Natotj/OctoMix/Documents/Display_Mount_Ideas.png

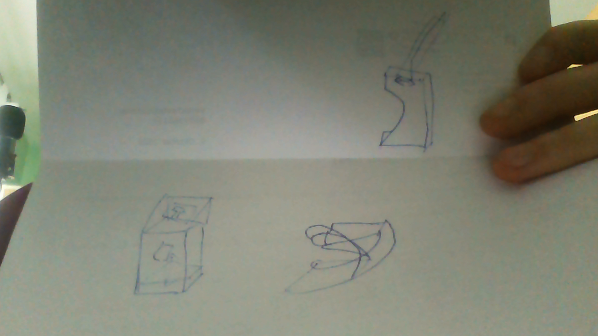
Documents/Display_Mount_Ideas.png
