Natotj/OctoMix/Main_Programming/Display/Design_Elements/Pages/Einstellungen.png

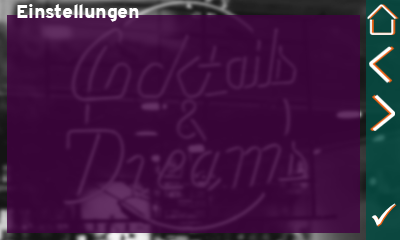
Main_Programming/Display/Design_Elements/Pages/Einstellungen.png
