Natotj/OctoMix/Main_Programming/Display/Design_Elements/Pages/Main.png

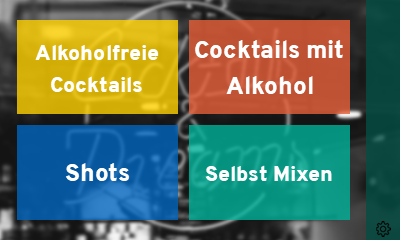
Main_Programming/Display/Design_Elements/Pages/Main.png
