Natotj/OctoMix/Main_Programming/Display/Design_Elements/Pages/Mix.png

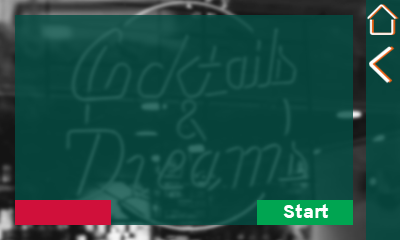
Main_Programming/Display/Design_Elements/Pages/Mix.png
