Natotj/OctoMix/Main_Programming/Display/Design_Elements/Pages/MIXMIX.png

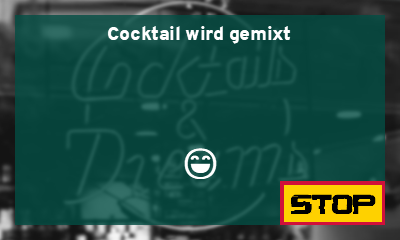
Main_Programming/Display/Design_Elements/Pages/MIXMIX.png
