Natotj/OctoMix/Main_Programming/Display/Design_Elements/Symbols/greenTransparentBG.png

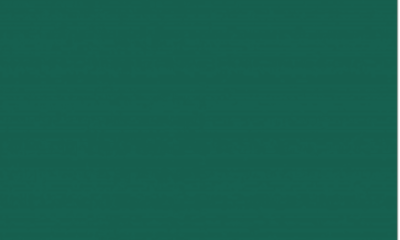
Main_Programming/Display/Design_Elements/Symbols/greenTransparentBG.png
