Natotj/OctoMix/Main_Programming/Display/Design_Elements/Symbols/haken.png

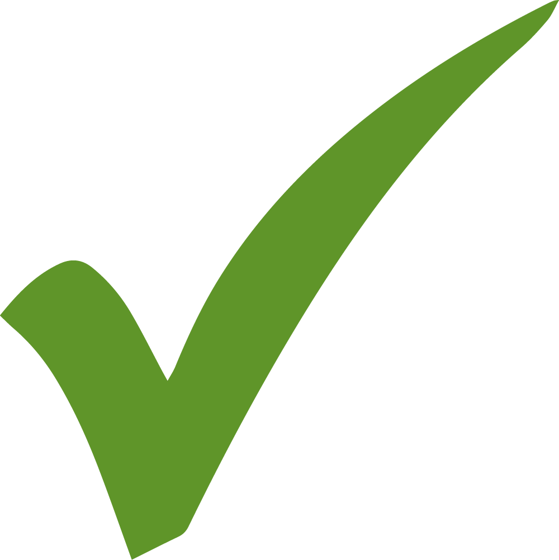
Main_Programming/Display/Design_Elements/Symbols/haken.png
