Natotj/OctoMix/Main_Programming/Display/Design_Elements/Symbols/haken_white.png

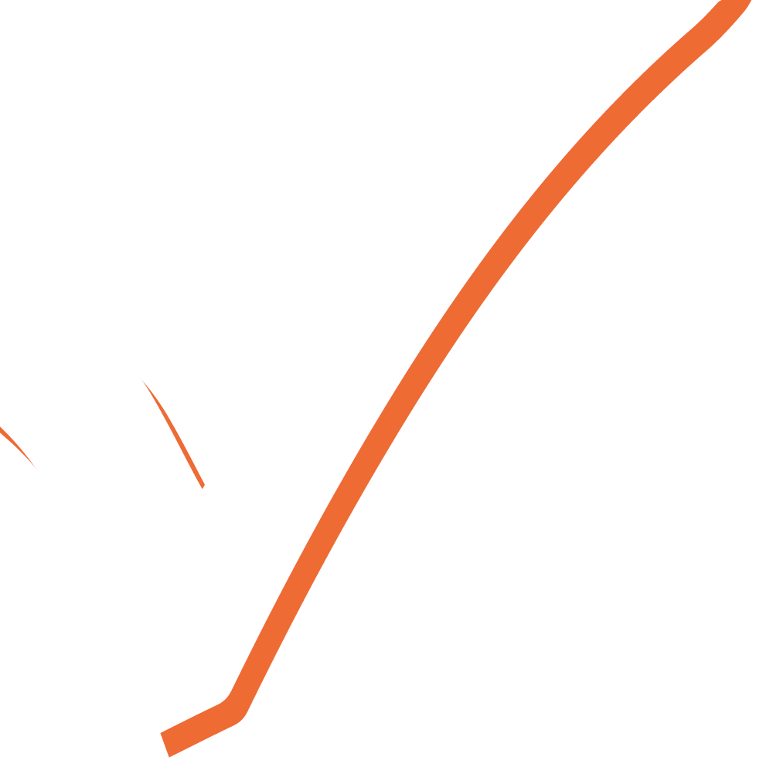
Main_Programming/Display/Design_Elements/Symbols/haken_white.png
