Natotj/OctoMix/Main_Programming/Display/Design_Elements/Symbols/warnung.png

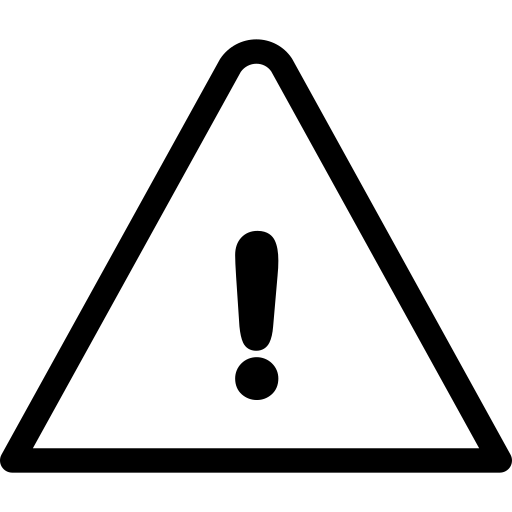
Main_Programming/Display/Design_Elements/Symbols/warnung.png
