Natotj/OctoMix/Main_Construction/3D-Print/Double Valve white.3mf

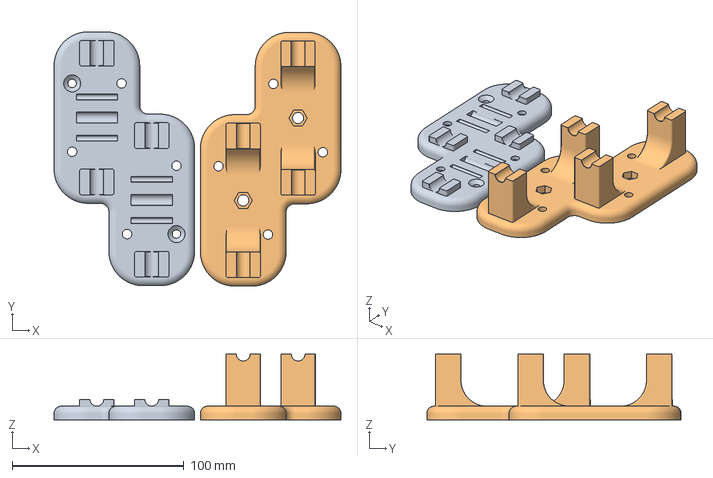
[picture p29: CAD file, 2024-12-11]
Main_Construction/3D-Print/Double Valve white.3mf
167.1 x 148.1 x 38.3 mm
valve_double_baseplate
valve_double_upper_frame
