Natotj/OctoMix/Main_Construction/3D-Print/ultrasonic_hc-sr04_-_face_mount.stp

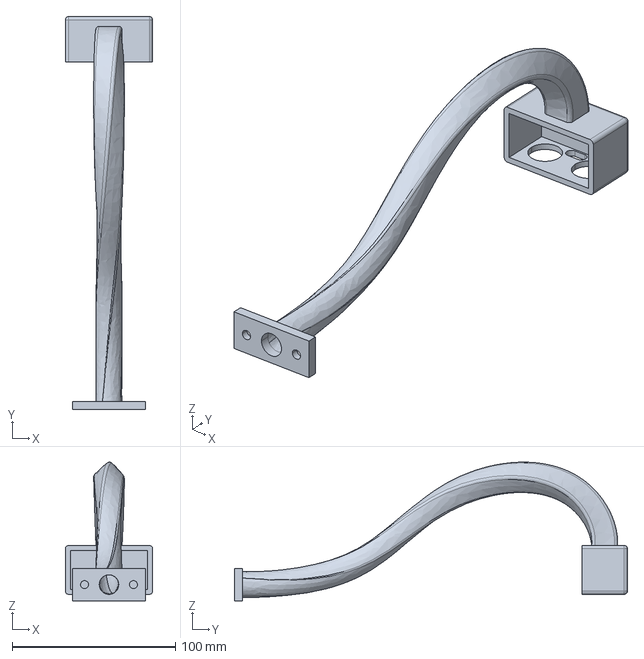
[picture p30: CAD file, 2024-12-06]
Main_Construction/3D-Print/ultrasonic_hc-sr04_-_face_mount.stp
53.5 x 241.1 x 85.1 mm
