Natotj/OctoMix/Main_Construction/3D-Print/ev3_stop.stp

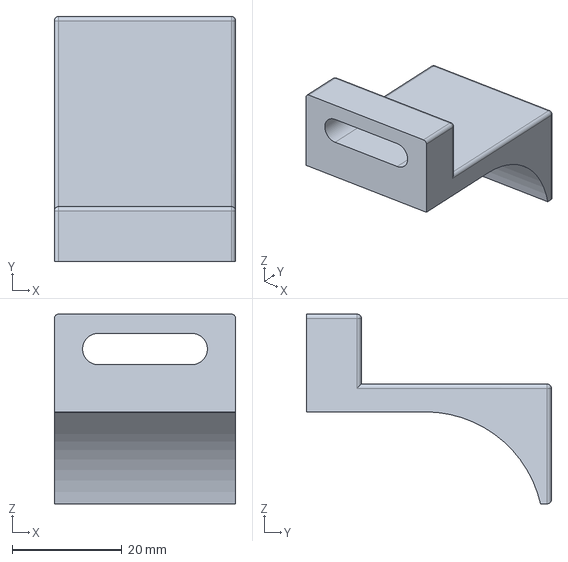
[picture p31: CAD file, 2024-11-20]
Main_Construction/3D-Print/ev3_stop.stp
33.0 x 44.6 x 34.5 mm
