Natotj/OctoMix/Main_Construction/3D-Print/hmi-top-part.stp

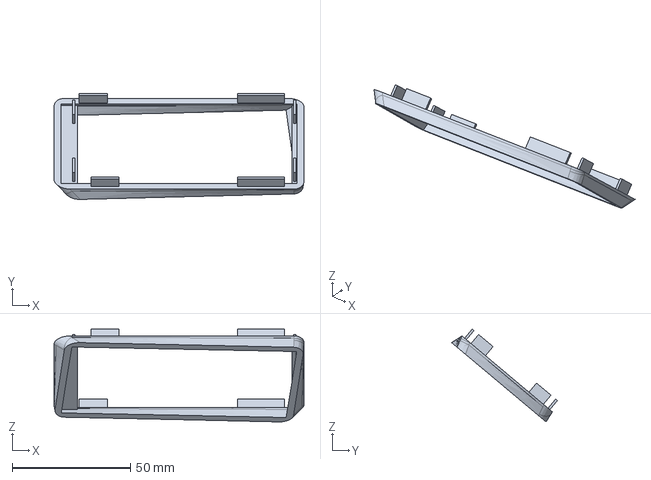
[picture p32: CAD file, 2024-11-20]
Main_Construction/3D-Print/hmi-top-part.stp
105.8 x 44.8 x 39.3 mm
