Natotj/OctoMix/Main_Construction/3D-Print/ev3_stop and Display braket and HMI top part.3mf

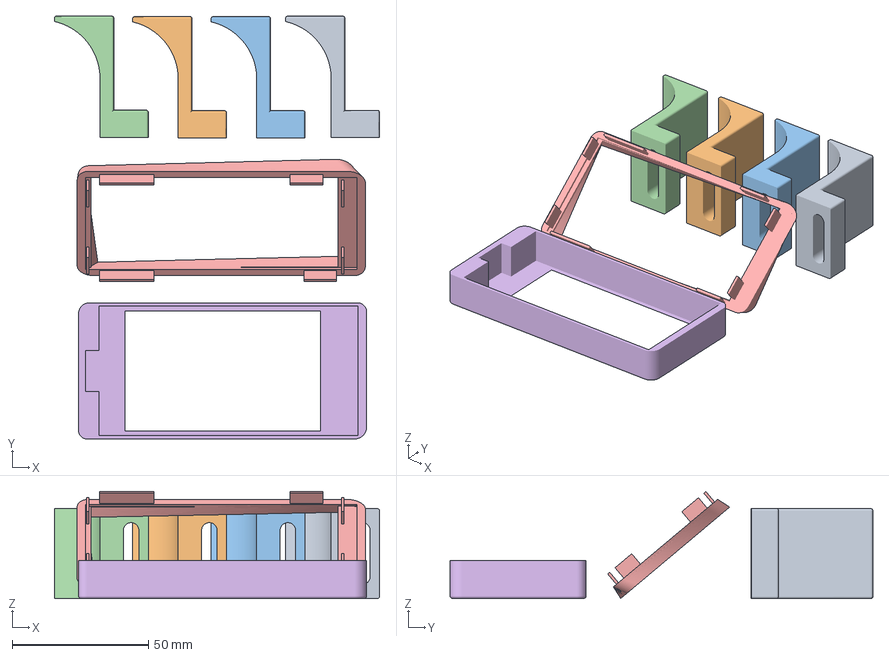
[picture p33: CAD file, 2024-11-20]
Main_Construction/3D-Print/ev3_stop and Display braket and HMI top part.3mf
119.3 x 155.1 x 39.2 mm
ev3_stop
hmi-top-part
display_braket
