Natotj/OctoMix/Main_Construction/3D-Print/Ultrasonic_Mount_upper_part.stp

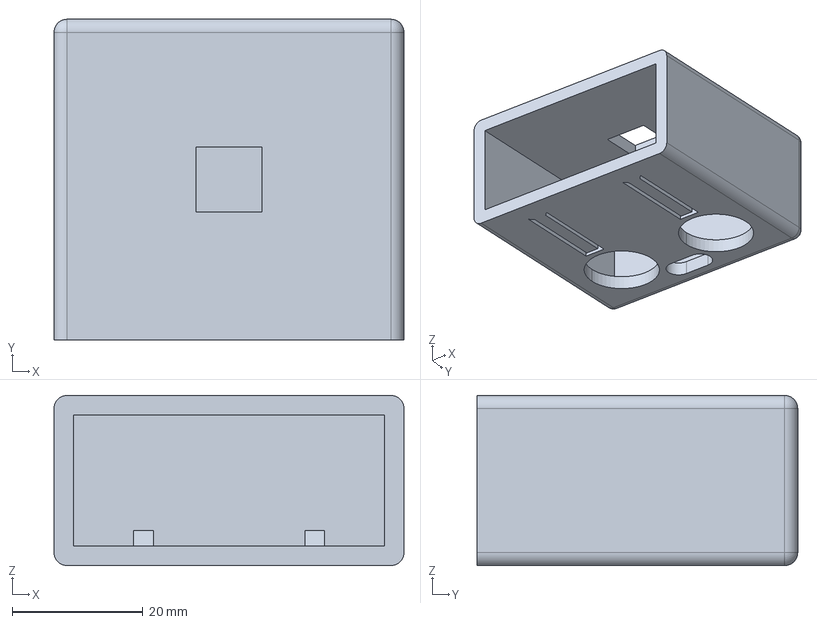
[picture p34: CAD file, 2024-11-18]
Main_Construction/3D-Print/Ultrasonic_Mount_upper_part.stp
53.5 x 49.0 x 26.0 mm
