Natotj/OctoMix/Main_Programming/Arduino/Arduino_Octomix/Display_Com.ino

// hier sind vier Funcitons! Display_Com (für die Kommunikaion generell),
// Display_Read (welche nur von Display_Com genutzt wird) zum lesen der vom Display gesendeten Daten
// Reset_Function um bei entsprechenden Display befehl neu zu starten
// Display_Write um auf das Display zu schreiben

void (*Reset_Func)(void) = 0; // Pointer auf Adresse 0 (Reset-Vektor) zum resetten vom Arduino

void Display_Com() {
// kommunikation mit dem Nextion Display

  String out="";
  unsigned char got=0;
  int i;
  char mark = '"';
// display Command 100: Cocktail ID wurde gesented erwaret crs
// display Command 101: crs_Mix wurde gesendet, Cocktail soll gemischt werden
// display Command 254: Arduino soll resettet werden
//  ID = 0;
  got = Display_Read();

  if(got>99){
// Cocktail ID empfangen und CRS senden

    if (got == 100) { // for receving a Cocktial ID and sending an Cocktail recipe
      do{
        ID = Display_Read();
      }while(ID<=0); //geht raus wenn falsch. Wenn über 0 dann geht weiter weil 1<=0 falsch ist
      // debug Info
      printLine("got ID");

      // Commands zum Display
      Display_Write_String("CRS.txt=", crs[ID-1]); // schreibt Variable CRS mit dem Cocktialrezept
      Display_Write_Number("tm0.en=", 1); // triggert das programm zum auflisten
    }

// crsMix empfangen
    if (got==101) { 
      printLine("Mixing");
      delay(50);
      for(i=0; i<sizeof(crsMix)/sizeof(crsMix[0]); i++){ //Muss vermutlich so geändert werden, dass immer geschaut wird ob etwas da ist und erst dann die schleife zuende führt
        crsMix[i] = Display_Read(); //Möglichkeit, dass Display read nichts empfangen hat und 0 schreibt
      }

      Display_Write_Number("Home.isMixing.val=", 1);
      isMixing = true;
    }

// Arduino reset
    if (got==254) {
      EV3_Com(EV3_STOP);
      Reset_Func();
    }
  }
}


unsigned char Display_Read(){
// liest den Seriellen port vom Display aus
  int index = 0;
  unsigned char buffer[4]; //4 weil 1x zeichen und 3x 0xFF (oder 0x00) je 2bytes

  if(displaySerial.available() >= 4){
    //Serial.print("Display= ");

    while(index < 4) { // liest immer vier stellen aus dem Buffer und return zum verarbeiten
      buffer[index] = displaySerial.read();
      /*
      Serial.print(buffer[index],HEX);
      Serial.print("\t");
      */
      index++;
    }
    //Serial.println(";");

/*
    if(buffer[4]==0x0FF){ //Endet ein Command mit FF, dann ist dieser ein Touch bzw. Page Event und nicht relevant
      buffer[0] = 0;
    } else {
      Serial.print("Display= ");
      Serial.println(buffer[0], HEX);
    }
    */
  } else buffer[0]=0;

return buffer[0];
}


void Display_Write_String(String command, String value){
// function that writes a string from the arduino to the display  
// command = the command you want to trigger 
// value = value that you want to transmitt to the command 
// for example: [String] "23021602089900000000000000000000" for Cool Brezze
  char mark='"';

  displaySerial.print(command);
  displaySerial.print(mark);
  displaySerial.print(value);
  displaySerial.print(mark);
    displayComandEnd();
}

void Display_Write_Number(String command, int value){
// function that writes a number from the arduino to the display  
// command = the command you want to trigger 
// value = value that you want to transmitt to the command 
// for example: 1 or 0 for on/off
  displaySerial.print(command);
  displaySerial.print(value);
    displayComandEnd();
}
