Natotj/OctoMix/Main_Programming/Arduino/Arduino_Octomix/Expanded_delay.ino

// function that takes in your desired delay & keeps otherthings (like the Display_Com()) upright
void Expanded_delay(int userDelay){

  for (int i = 0; i < userDelay; i += 51){
    Display_Com();
    delay(50);
  }
  // rest of the user delay
  delay(userDelay % 100);
}
